gyrrei/IN2106_MicroMouse/src/Code/pwm.c

/*
 * File:   pwm.c
 * Author: Steff
 *
 * Created on 11. Juni 2019, 18:31
 * Changed by Adrian on 5-7-2019
 * 
 */

#include "xc.h"
#include "gpio.h"
#include "dma.h"
#include <stdio.h>
#include "qei.h"
#include "control.h"
#include "pwm.h"

void init_PWM()
{

    /*~~~~~~~~~~~~~~~~~~~~~~~ PWM1 Configuration ~~~~~~~~~~~~~~~~~~~~~~~~~~~~*/

    P1TCONbits.PTEN = 0; //Disable the PWM Module for configuration
    P2TCONbits.PTEN = 0;

    P1TCONbits.PTMOD = 0; // Define free running mode for PWM 1
    P2TCONbits.PTMOD = 0;

    PWM1CON1bits.PMOD1 = 1; // Define independent mode for PWM output pair 1
    //PWM1CON1bits.PMOD2 = 1; // Define independent mode for PWM output pair 2
    PWM2CON1bits.PMOD1 = 1;
    

    P1TPERbits.PTPER = 2000; // PWM will count "up to 100" before resetting
    P2TPERbits.PTPER = 2000;

    /* THIS IS THE KEY VARIABLE TO CHANGE SPEED WITH
	* The duty cycle basically calculates as:
	* P1DC1/PxTPERbits.PTPER , where x denotes the number of the PWM module
	* Raising PxDCy increases speed and vice versa.
	* Here, x stands for the PWM module number and y for the PWM output channel
	* number of that module
	* Raising PTPER allows smaller increments (e.g. 100 allows increments of 1/100)
	* but makes the puls width bigger, decreasing smoothness of V curve
	*/
    P1DC1 = 1000; // PWM output will be active till count goes to 1000
    P2DC1 = 1000;

    //P1DC2 = 1000; // PWM output will be active till count goes to 1000

    PWM1CON1bits.PEN1H = 0; // PWM1H is controlled by GPIO module
    PWM1CON1bits.PEN1L = 1; // PWM1L is controlled by PWM module
    // PIN 26 is used as PWM output PIN for motor 1 (can be removed?))

    PWM2CON1bits.PEN1H = 0; // PWM2H is controlled by GPIO module
    PWM2CON1bits.PEN1L = 1; // PWM2L is controlled by PWM module
    // PIN 24 is used as PWM output PIN for motor 2 (can be removed?))

    P1TCONbits.PTEN = 1; // Enable the PWM Module
    P2TCONbits.PTEN = 1;    
        
    // No deadtime inserted yet, as it seems irrelevant right now
}

void drive_motor(char motor, int dutycycle)
{
    if (dutycycle > 0) {
        drive_motor_forward(motor, dutycycle);
    } else if (dutycycle < 0) {
        drive_motor_backward(motor, -dutycycle);
    } else {
        fast_stop_motor(motor);
    }
}

void drive_motor_forward(char motor, int dutycycle)
{
    if (motor == 'L'){
        HBRIDGE1 = 0;
        HBRIDGE2 = 1;
        P1DC1 = dutycycle;
    } else if (motor == 'R'){
        HBRIDGE3 = 0;
        HBRIDGE4 = 1;
        P2DC1 = dutycycle;
    }
}

void drive_motor_backward(char motor, int dutycycle)
{
    if (motor == 'L'){
        HBRIDGE1 = 1;
        HBRIDGE2 = 0;
        P1DC1 = dutycycle;
    } else if (motor == 'R'){
        HBRIDGE3 = 1;
        HBRIDGE4 = 0;
        P2DC1 = dutycycle;
    }
}

void fast_stop_motor(char motor)
{
    if (motor == 'L'){
        HBRIDGE1 = HBRIDGE2;
    } else if (motor == 'R'){
        HBRIDGE3 = HBRIDGE4;
    }
}
