gyrrei/IN2106_MicroMouse/src/Code/adc.h

/* 
 * File:   adc.h
 * Author: a2-lenz
 *
 * Created on December 10, 2018, 4:59 PM
 */

#ifndef ADC_H
#define ADC_H

#ifdef __cplusplus
extern "C"
{
#endif
    
    void setupADC1(void);
    void startADC1(void);

#ifdef __cplusplus
}
#endif

#endif 
